bagus-Arya/fishdryer/Laporan kemajuan fisheris/foto/depan.jpg

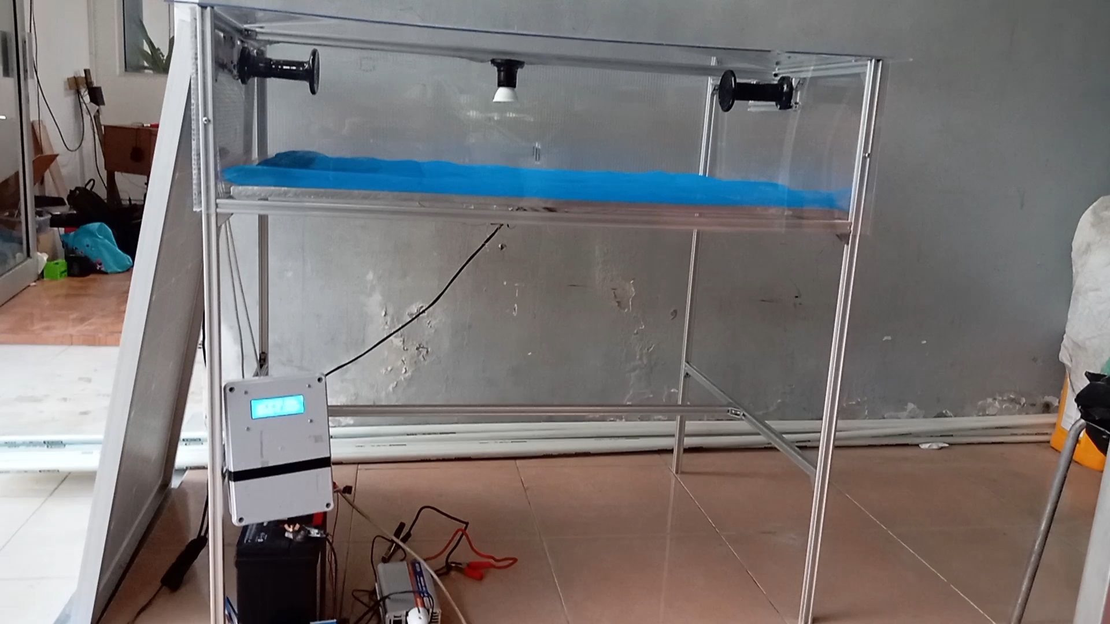
Laporan kemajuan fisheris/foto/depan.jpg
