bagus-Arya/fishdryer/Laporan kemajuan fisheris/foto/depan.png

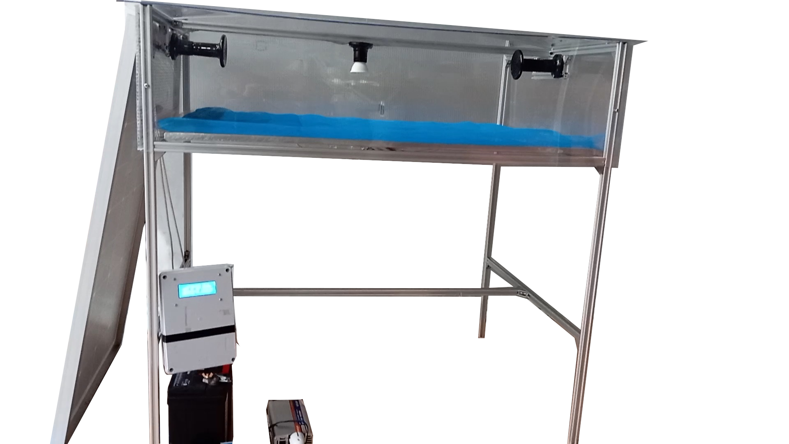
Laporan kemajuan fisheris/foto/depan.png
