bagus-Arya/fishdryer/Laporan kemajuan fisheris/foto/IMG_20220815_173028_107.jpg

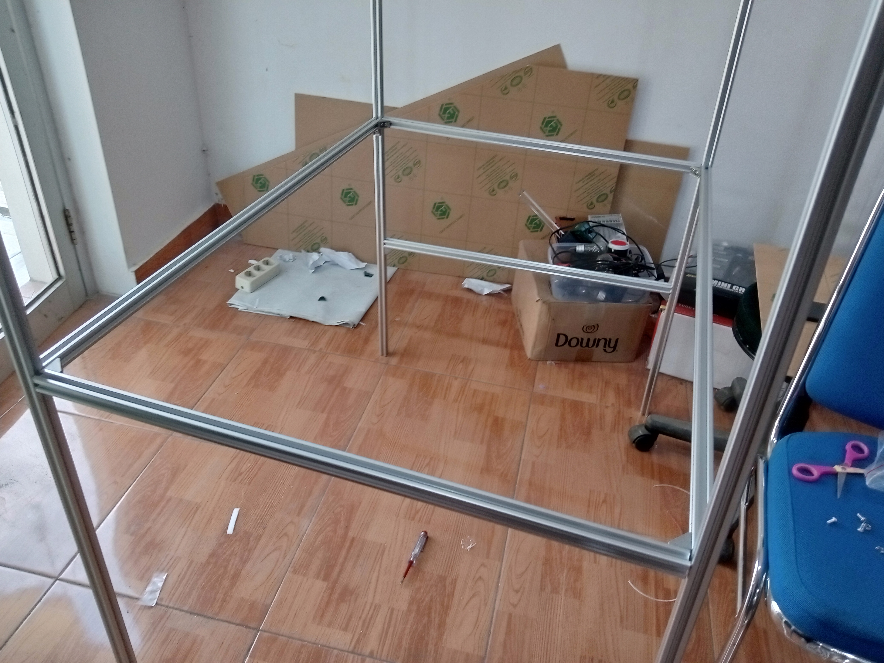
Laporan kemajuan fisheris/foto/IMG_20220815_173028_107.jpg
