bagus-Arya/fishdryer/Laporan kemajuan fisheris/foto/IMG_20220815_173037_453.jpg

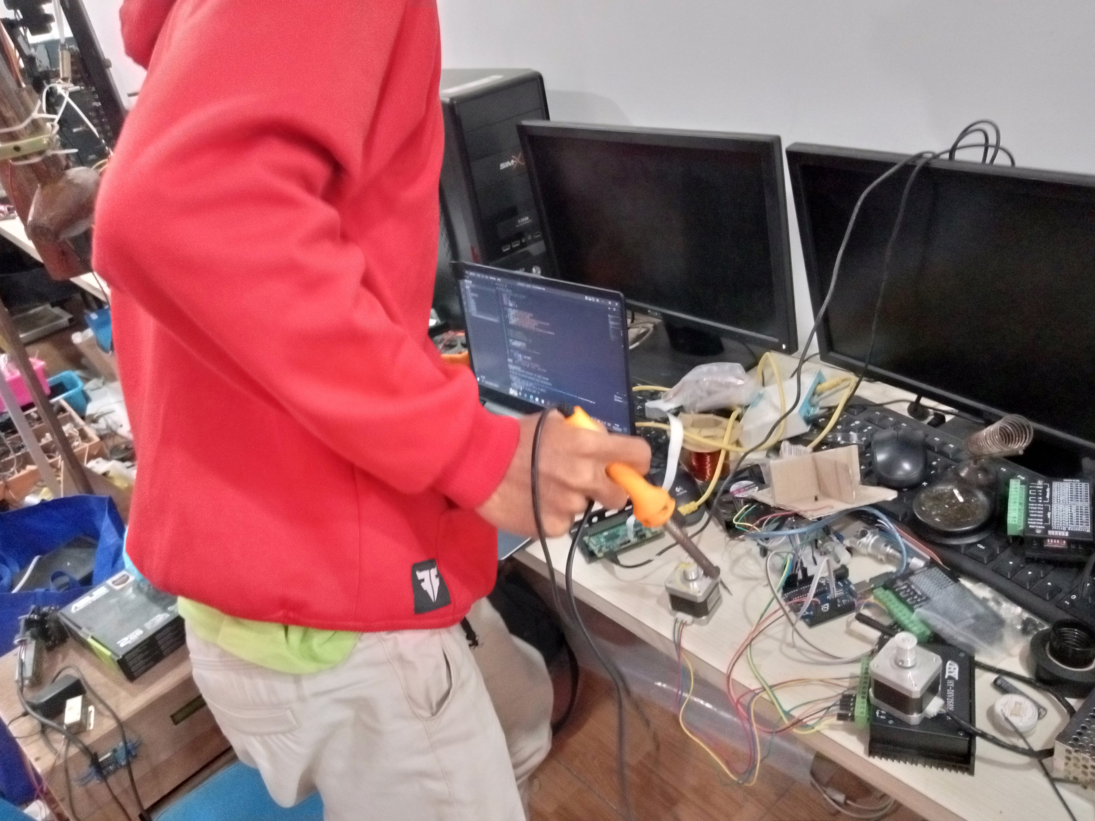
Laporan kemajuan fisheris/foto/IMG_20220815_173037_453.jpg
