bagus-Arya/fishdryer/Laporan kemajuan fisheris/foto/IMG_20220815_173118_141.jpg

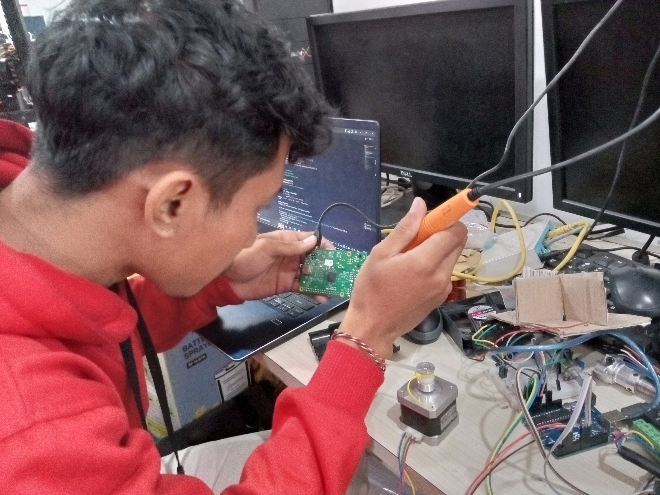
Laporan kemajuan fisheris/foto/IMG_20220815_173118_141.jpg
