bagus-Arya/fishdryer/Laporan kemajuan fisheris/foto/IMG_20220818_150203_695.jpg

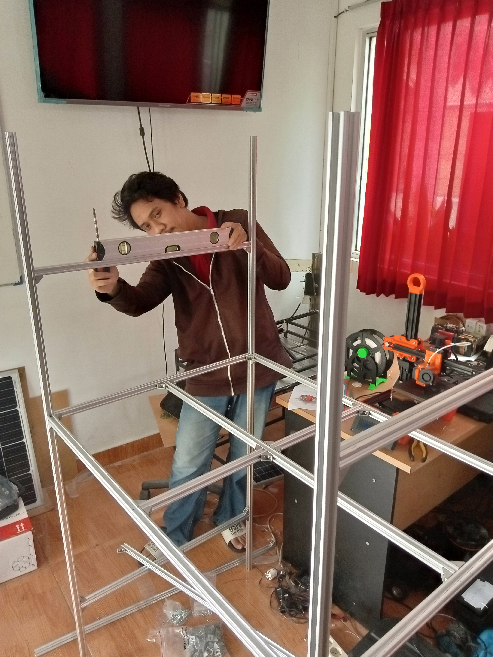
Laporan kemajuan fisheris/foto/IMG_20220818_150203_695.jpg
