bagus-Arya/fishdryer/Laporan kemajuan fisheris/foto/IMG_20220820_165152_122.jpg

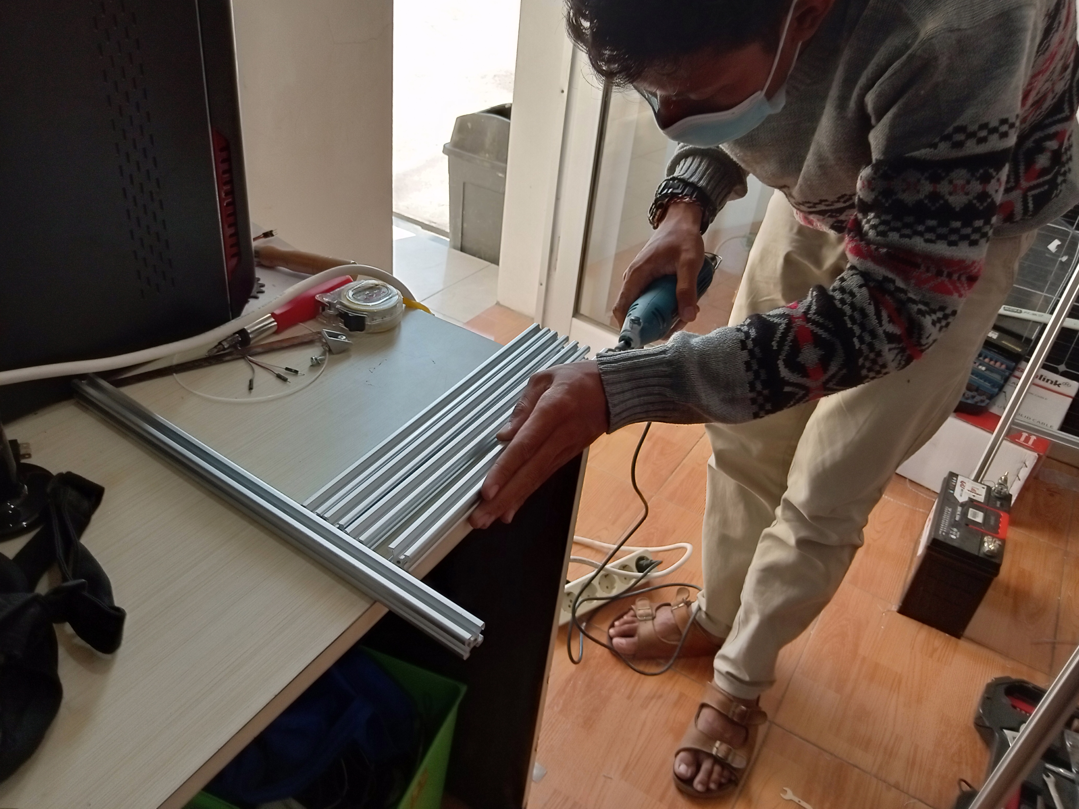
Laporan kemajuan fisheris/foto/IMG_20220820_165152_122.jpg
