bagus-Arya/fishdryer/Laporan kemajuan fisheris/foto/IMG_20220826_161308_476.jpg

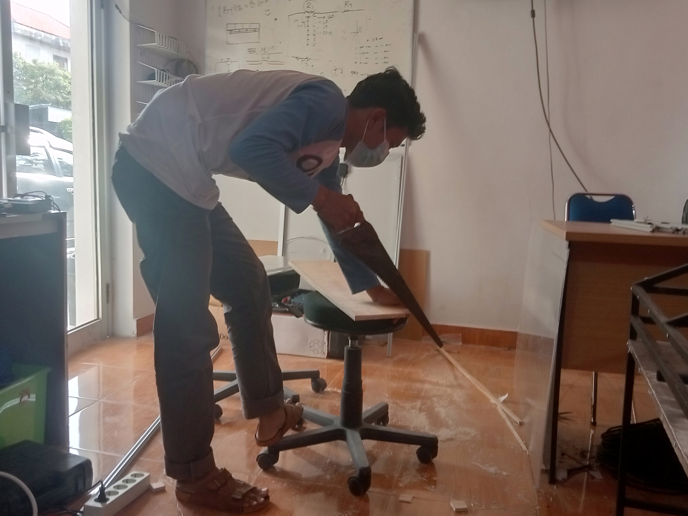
Laporan kemajuan fisheris/foto/IMG_20220826_161308_476.jpg
