bagus-Arya/fishdryer/Laporan kemajuan fisheris/foto/IMG_20220826_161310_042.jpg

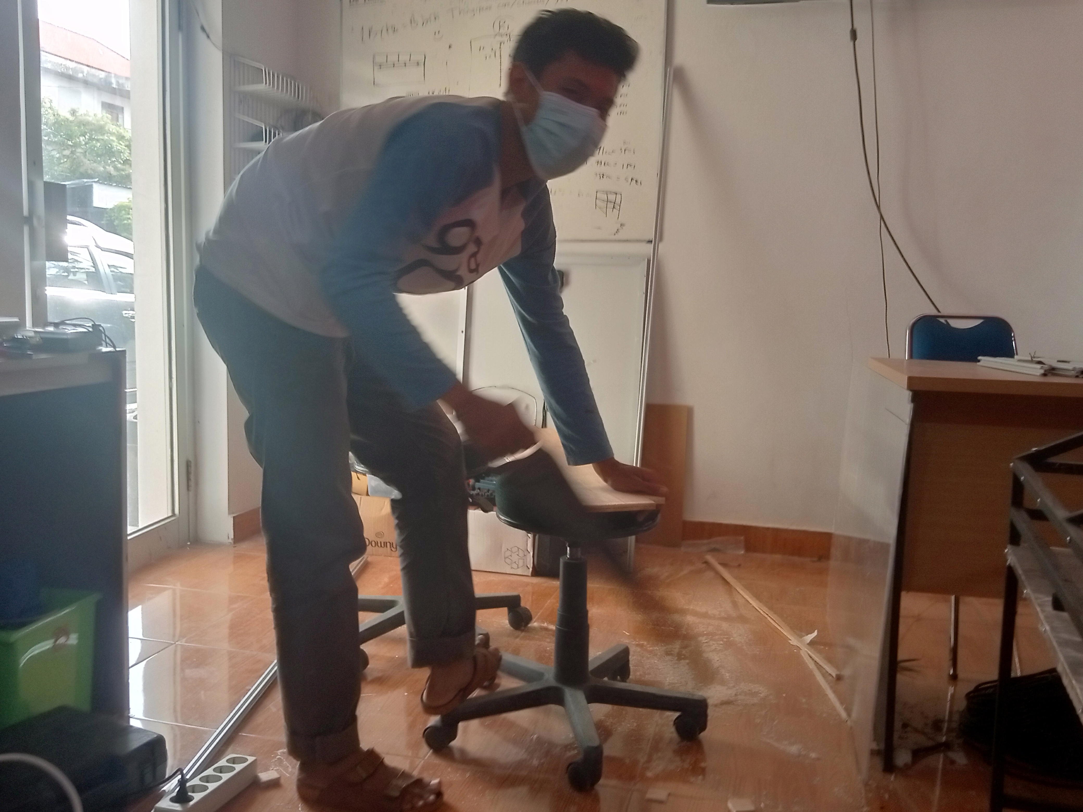
Laporan kemajuan fisheris/foto/IMG_20220826_161310_042.jpg
