bagus-Arya/fishdryer/Laporan kemajuan fisheris/foto/IMG_20220901_162546_568.jpg

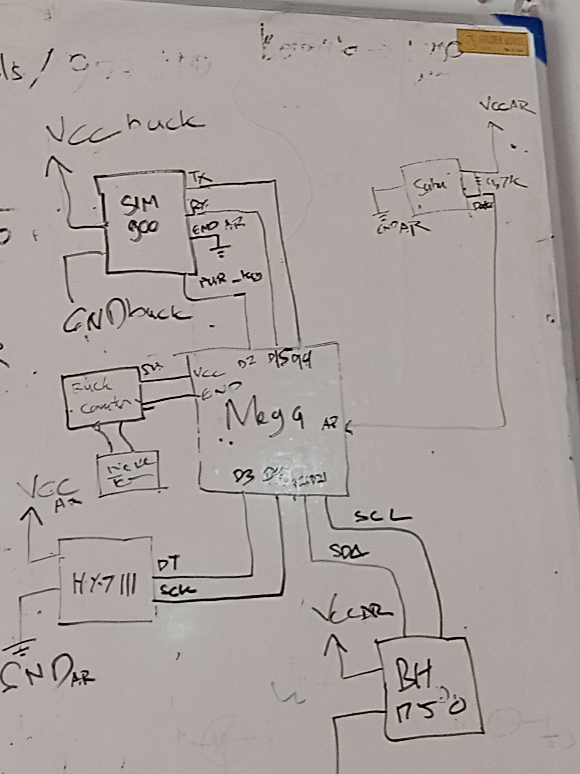
Laporan kemajuan fisheris/foto/IMG_20220901_162546_568.jpg
