bagus-Arya/fishdryer/Laporan kemajuan fisheris/foto/IMG_20220907_133712_170.jpg

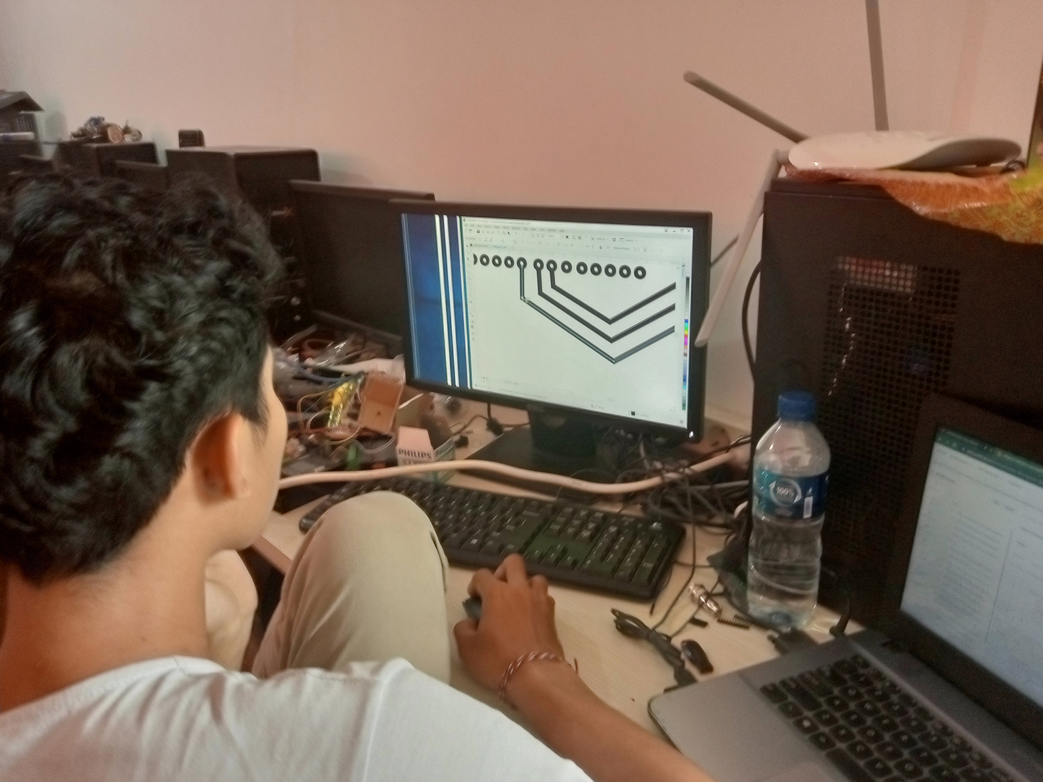
Laporan kemajuan fisheris/foto/IMG_20220907_133712_170.jpg
