bagus-Arya/fishdryer/Laporan kemajuan fisheris/foto/IMG_20220916_162647_596.jpg

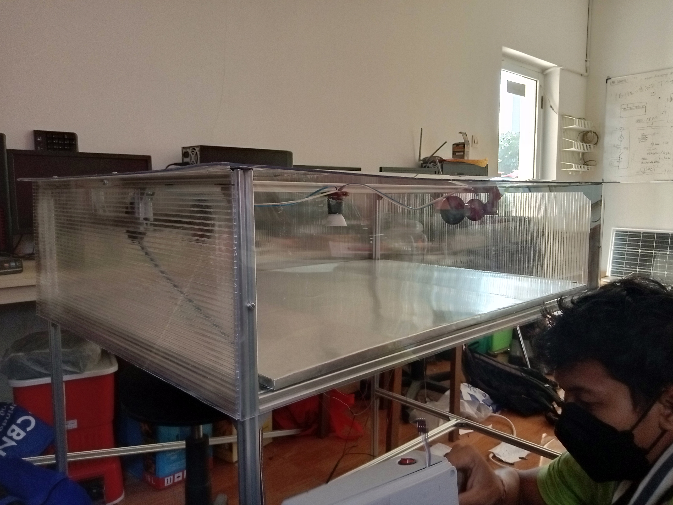
Laporan kemajuan fisheris/foto/IMG_20220916_162647_596.jpg
