bagus-Arya/fishdryer/Laporan kemajuan fisheris/foto/IMG_20220916_162656_175.jpg

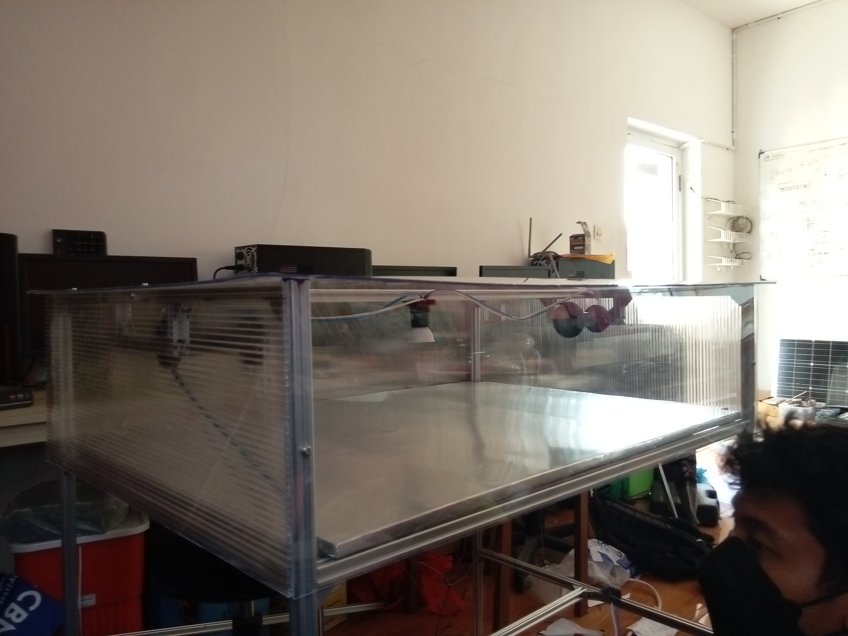
Laporan kemajuan fisheris/foto/IMG_20220916_162656_175.jpg
