bagus-Arya/fishdryer/Laporan kemajuan fisheris/foto/IMG_20220916_162714_745.jpg

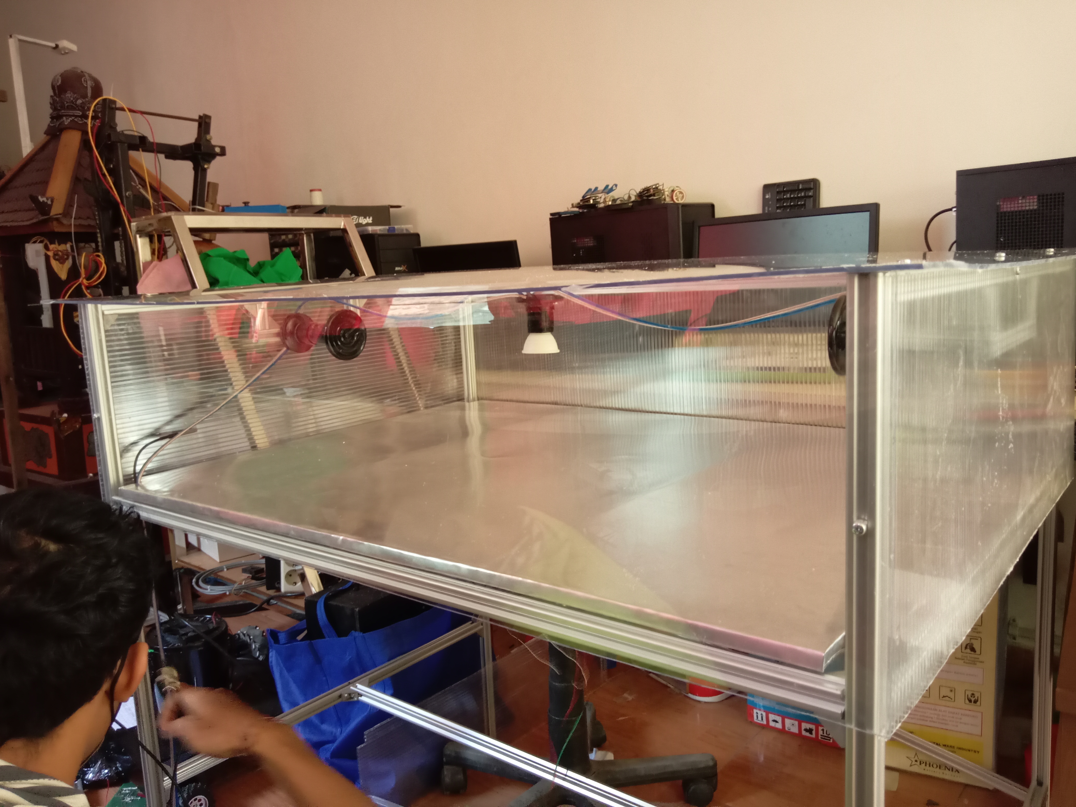
Laporan kemajuan fisheris/foto/IMG_20220916_162714_745.jpg
