bagus-Arya/fishdryer/Laporan kemajuan fisheris/foto/IMG_20220916_162727_313.jpg

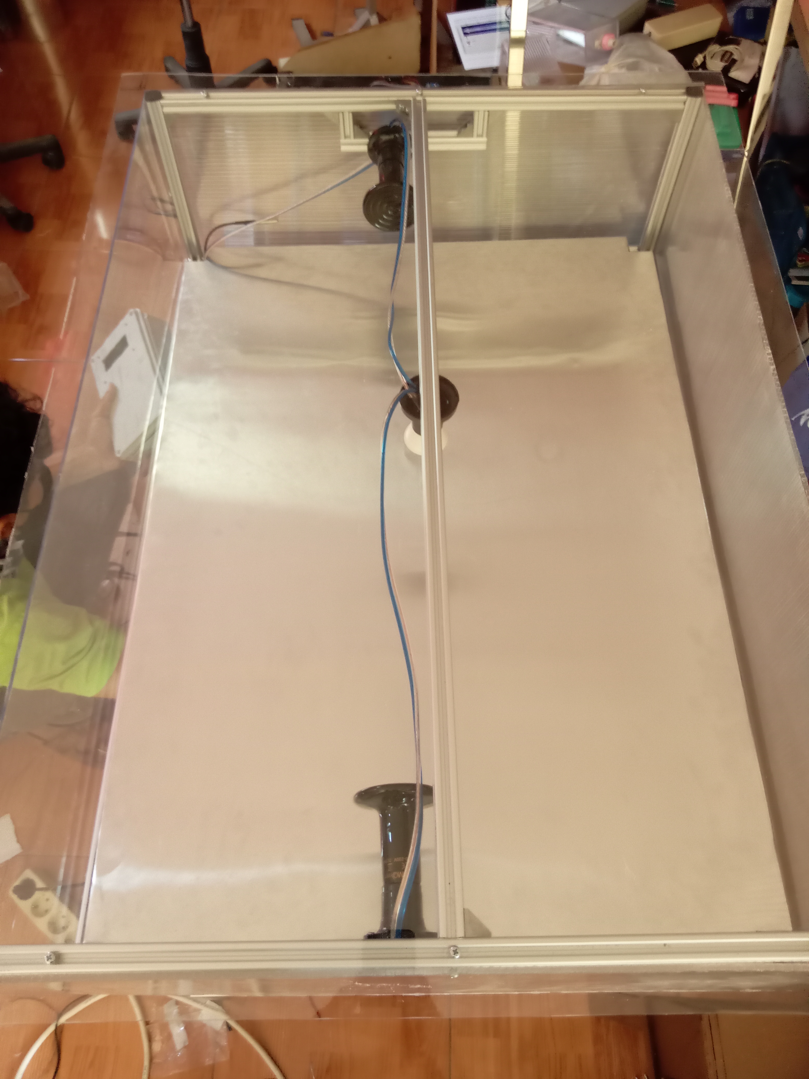
Laporan kemajuan fisheris/foto/IMG_20220916_162727_313.jpg
