bagus-Arya/fishdryer/Laporan kemajuan fisheris/foto/IMG_20220916_162906_557.jpg

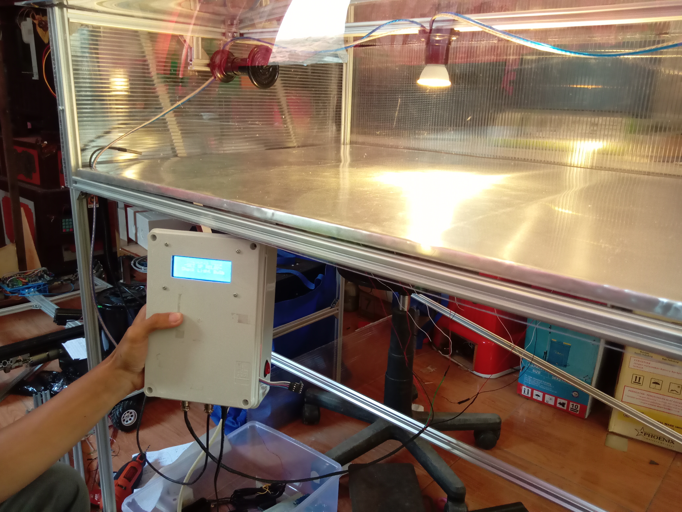
Laporan kemajuan fisheris/foto/IMG_20220916_162906_557.jpg
