bagus-Arya/fishdryer/Laporan kemajuan fisheris/foto/IMG_20220916_162908_476.jpg

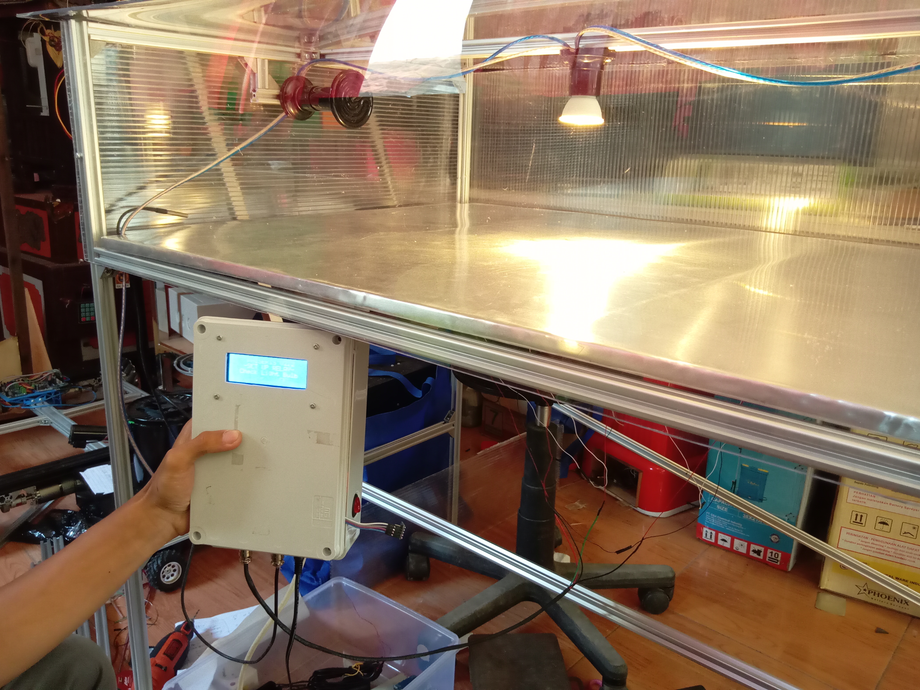
Laporan kemajuan fisheris/foto/IMG_20220916_162908_476.jpg
