bagus-Arya/fishdryer/Laporan kemajuan fisheris/foto/IMG_20220916_162945_065.jpg

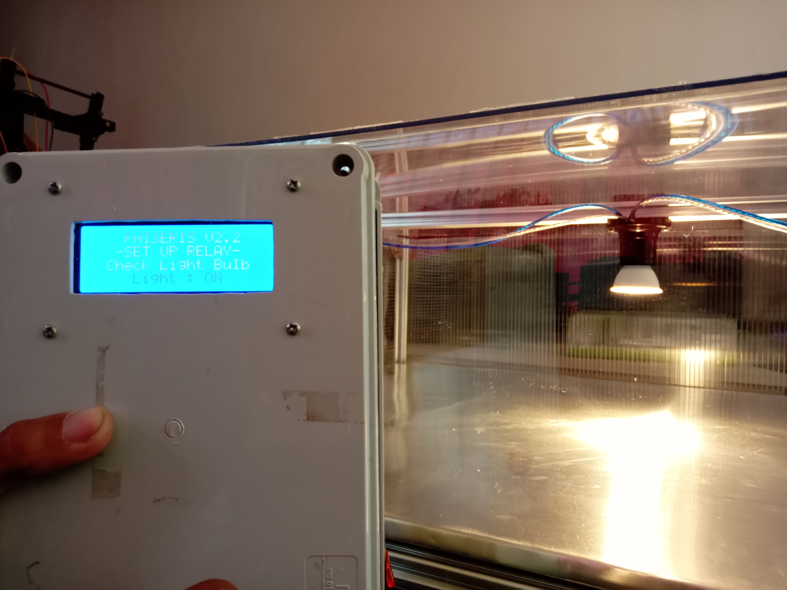
Laporan kemajuan fisheris/foto/IMG_20220916_162945_065.jpg
