bagus-Arya/fishdryer/Laporan kemajuan fisheris/foto/IMG_20220916_162948_088.jpg

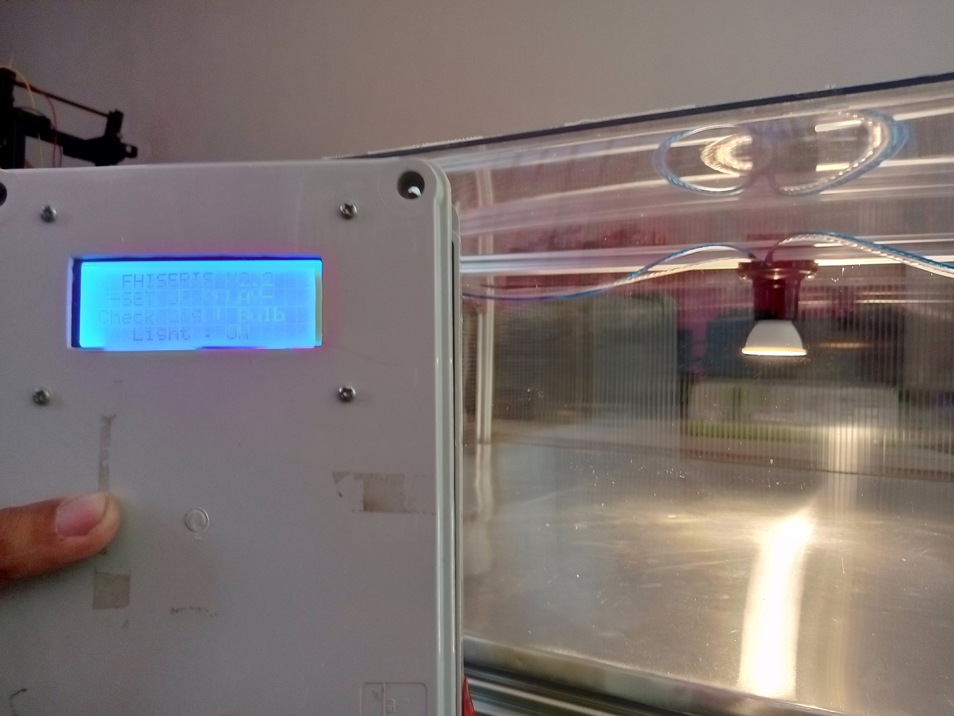
Laporan kemajuan fisheris/foto/IMG_20220916_162948_088.jpg
