bagus-Arya/fishdryer/Laporan kemajuan fisheris/foto/IMG_20220917_181628_784.jpg

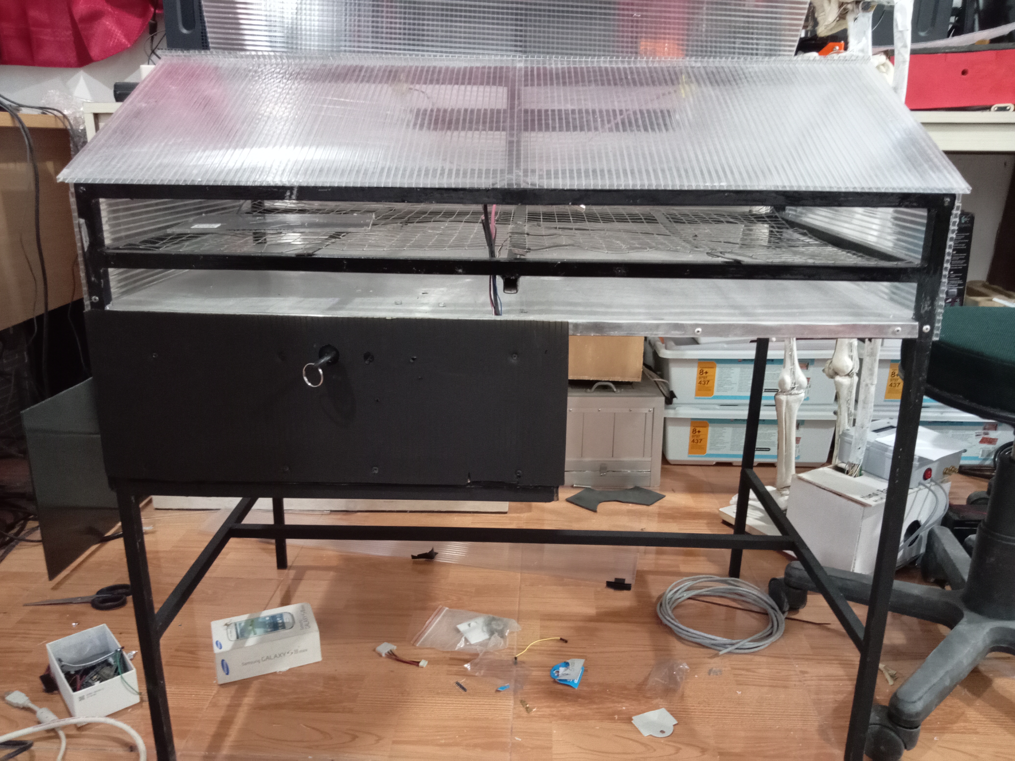
Laporan kemajuan fisheris/foto/IMG_20220917_181628_784.jpg
