bagus-Arya/fishdryer/Laporan kemajuan fisheris/foto/IMG_20220917_181641_316.jpg

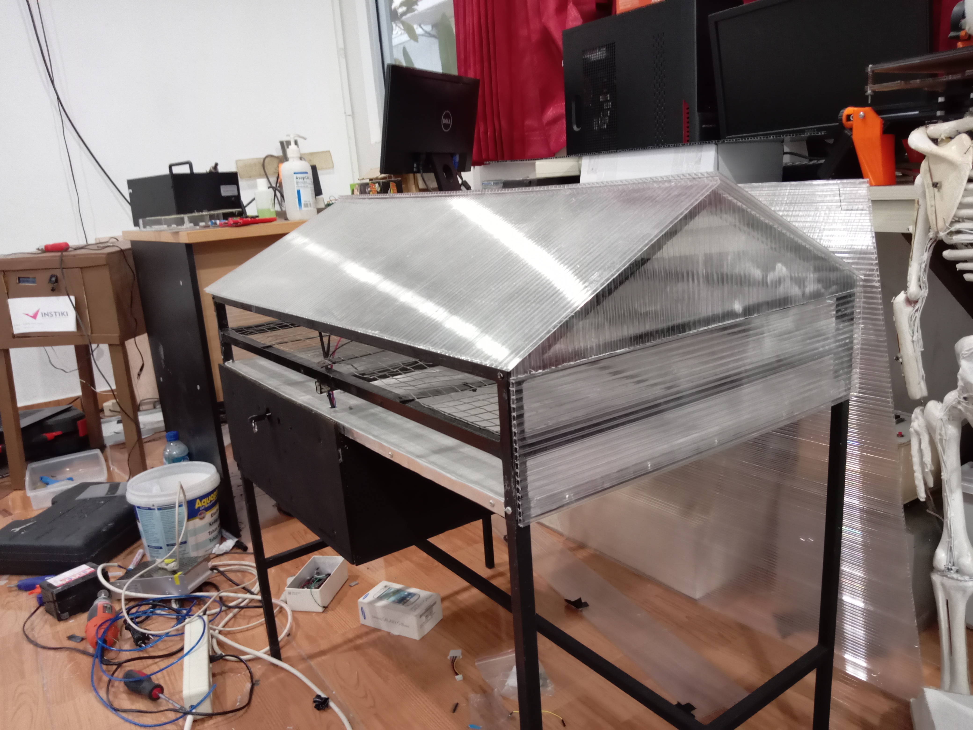
Laporan kemajuan fisheris/foto/IMG_20220917_181641_316.jpg
