bagus-Arya/fishdryer/Laporan kemajuan fisheris/foto/IMG_20220917_181651_541.jpg

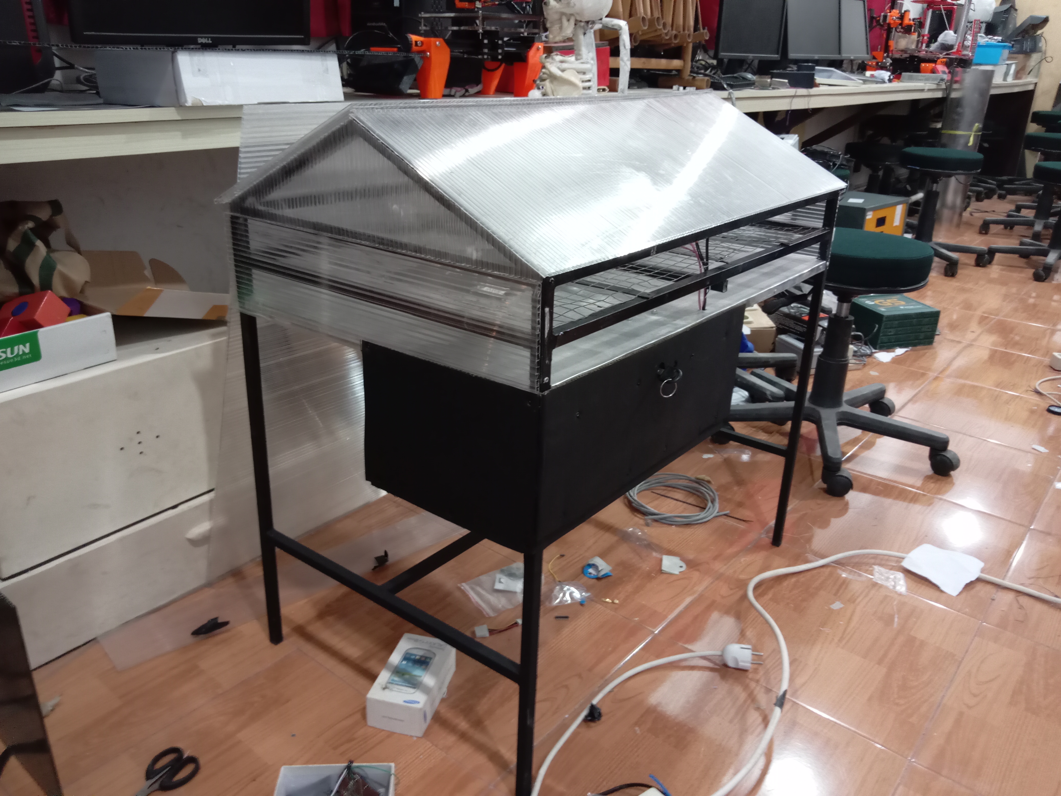
Laporan kemajuan fisheris/foto/IMG_20220917_181651_541.jpg
