bagus-Arya/fishdryer/Laporan kemajuan fisheris/foto/PCB.png

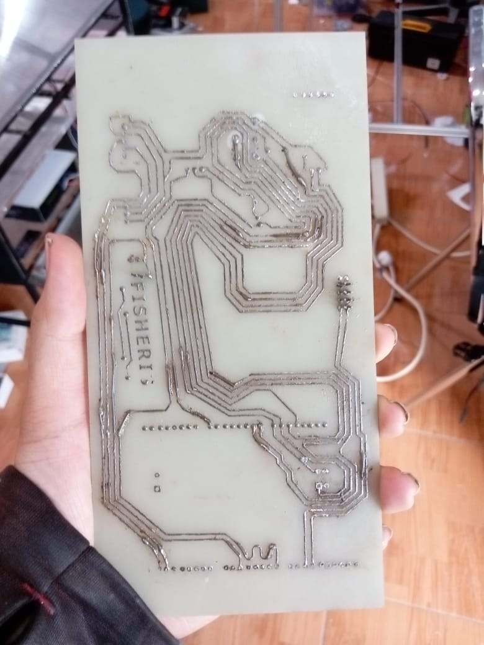
Laporan kemajuan fisheris/foto/PCB.png
