bagus-Arya/fishdryer/Laporan kemajuan fisheris/foto/samping.png

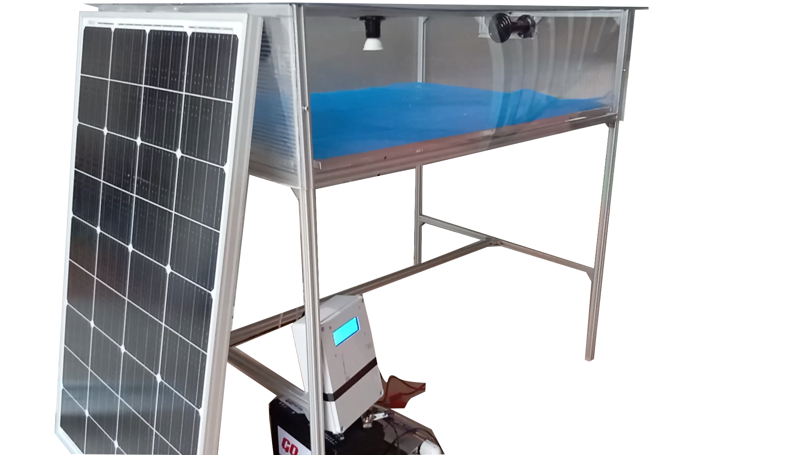
Laporan kemajuan fisheris/foto/samping.png
