bagus-Arya/fishdryer/Laporan kemajuan fisheris/skema.jpg

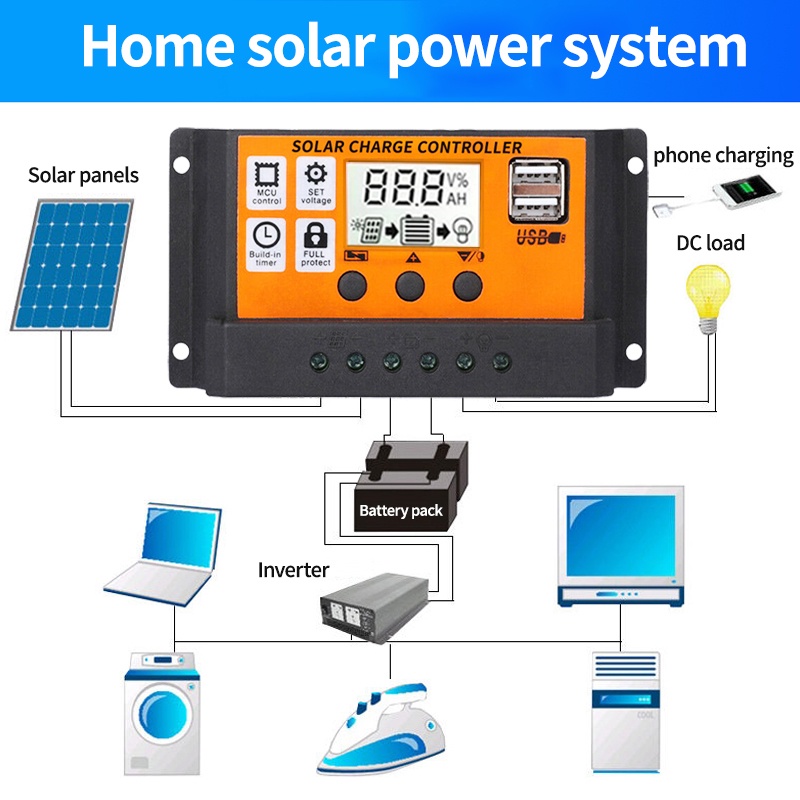
Laporan kemajuan fisheris/skema.jpg
