bagus-Arya/fishdryer/arduinocode/Fisheris V2.3/code/lcd/HelloWorld/HelloWorld.ino

#include <Wire.h> 
#include <LiquidCrystal_I2C.h>

// Set the LCD address to 0x27 for a 16 chars and 2 line display
LiquidCrystal_I2C lcd(0x27, 20, 4);

void setup()
{
	// initialize the LCD
	lcd.begin();

	// Turn on the blacklight and print a message.
	lcd.backlight();
  lcd.setCursor(1,0);//colom,baris
	lcd.print("Hello, world!");
}

void loop()
{
	// Do nothing here...
}
